deltabeard/DBGC/sw/gb_manager/inc/rom_512kb.gb.h

static const unsigned char rom_512kb_gb[] = {
  0x00, 0xff, 0xff, 0xff, 0xff, 0xff, 0xff, 0xff, 0xff, 0xff, 0xff, 0xff,
  0xff, 0xff, 0xff, 0xff, 0xff, 0xff, 0xff, 0xff, 0xff, 0xff, 0xff, 0xff,
  0xff, 0xff, 0xff, 0xff, 0xff, 0xff, 0xff, 0xff, 0xff, 0xff, 0xff, 0xff,
  0xff, 0xff, 0xff, 0xff, 0xff, 0xff, 0xff, 0xff, 0xff, 0xff, 0xff, 0xff,
  0xff, 0xff, 0xff, 0xff, 0xff, 0xff, 0xff, 0xff, 0xff, 0xff, 0xff, 0xff,
  0xff, 0xff, 0xff, 0xff, 0xff, 0xff, 0xff, 0xff, 0xff, 0xff, 0xff, 0xff,
  0xff, 0xff, 0xff, 0xff, 0xff, 0xff, 0xff, 0xff, 0xff, 0xff, 0xff, 0xff,
  0xff, 0xff, 0xff, 0xff, 0xff, 0xff, 0xff, 0xff, 0xff, 0xff, 0xff, 0xff,
  0xff, 0xff, 0xff, 0xff, 0xff, 0xff, 0xff, 0xff, 0xff, 0xff, 0xff, 0xff,
  0xff, 0xff, 0xff, 0xff, 0xff, 0xff, 0xff, 0xff, 0xff, 0xff, 0xff, 0xff,
  0xff, 0xff, 0xff, 0xff, 0xff, 0xff, 0xff, 0xff, 0xff, 0xff, 0xff, 0xff,
  0xff, 0xff, 0xff, 0xff, 0xff, 0xff, 0xff, 0xff, 0xff, 0xff, 0xff, 0xff,
  0xff, 0xff, 0xff, 0xff, 0xff, 0xff, 0xff, 0xff, 0xff, 0xff, 0xff, 0xff,
  0xff, 0xff, 0xff, 0xff, 0xff, 0xff, 0xff, 0xff, 0xff, 0xff, 0xff, 0xff,
  0xff, 0xff, 0xff, 0xff, 0xff, 0xff, 0xff, 0xff, 0xff, 0xff, 0xff, 0xff,
  0xff, 0xff, 0xff, 0xff, 0xff, 0xff, 0xff, 0xff, 0xff, 0xff, 0xff, 0xff,
  0xff, 0xff, 0xff, 0xff, 0xff, 0xff, 0xff, 0xff, 0xff, 0xff, 0xff, 0xff,
  0xff, 0xff, 0xff, 0xff, 0xff, 0xff, 0xff, 0xff, 0xff, 0xff, 0xff, 0xff,
  0xff, 0xff, 0xff, 0xff, 0xff, 0xff, 0xff, 0xff, 0xff, 0xff, 0xff, 0xff,
  0xff, 0xff, 0xff, 0xff, 0xff, 0xff, 0xff, 0xff, 0xff, 0xff, 0xff, 0xff,
  0xff, 0xff, 0xff, 0xff, 0xff, 0xff, 0xff, 0xff, 0xff, 0xff, 0xff, 0xff,
  0xff, 0xff, 0xff, 0xff, 0x00, 0xc3, 0x50, 0x01, 0xce, 0xed, 0x66, 0x66,
  0xcc, 0x0d, 0x00, 0x0b, 0x03, 0x73, 0x00, 0x83, 0x00, 0x0c, 0x00, 0x0d,
  0x00, 0x08, 0x11, 0x1f, 0x88, 0x89, 0x00, 0x0e, 0xdc, 0xcc, 0x6e, 0xe6,
  0xdd, 0xdd, 0xd9, 0x99, 0xbb, 0xbb, 0x67, 0x63, 0x6e, 0x0e, 0xec, 0xcc,
  0xdd, 0xdc, 0x99, 0x9f, 0xbb, 0xb9, 0x33, 0x3e, 0x6d, 0x6f, 0x6f, 0x6e,
  0x65, 0x79, 0x65, 0x2d, 0x67, 0x62, 0x20, 0x74, 0x65, 0x73, 0x74, 0x00,
  0x5a, 0x5a, 0x00, 0x01, 0x01, 0x00, 0x01, 0x33, 0x00, 0x2b, 0x88, 0x04,
  0x31, 0x00, 0xe0, 0x21, 0x00, 0xc0, 0x11, 0x0e, 0x02, 0x01, 0xa0, 0x00,
  0xcd, 0xda, 0x48, 0x21, 0x00, 0xc2, 0x11, 0xae, 0x02, 0x01, 0x80, 0x01,
  0xcd, 0xda, 0x48, 0xc3, 0x00, 0xc0, 0xf3, 0x21, 0x75, 0x01, 0xc3, 0xf1,
  0x47, 0xcd, 0xf3, 0x48, 0x54, 0x45, 0x53, 0x54, 0x20, 0x46, 0x41, 0x49,
  0x4c, 0x45, 0x44, 0x00, 0xcd, 0xbb, 0x48, 0xf0, 0x83, 0xa7, 0x20, 0x11,
  0xcd, 0xf3, 0x48, 0x24, 0x30, 0x30, 0x30, 0x30, 0x2d, 0x24, 0x33, 0x46,
  0x46, 0x46, 0x00, 0x18, 0x0f, 0xcd, 0xf3, 0x48, 0x24, 0x34, 0x30, 0x30,
  0x30, 0x2d, 0x24, 0x37, 0x46, 0x46, 0x46, 0x00, 0xcd, 0xbb, 0x48, 0xcd,
  0xf3, 0x48, 0x4d, 0x4f, 0x44, 0x45, 0x20, 0x00, 0xf0, 0x84, 0xcd, 0xd0,
  0x48, 0xcd, 0xbb, 0x48, 0xcd, 0xbb, 0x48, 0xcd, 0xf3, 0x48, 0x42, 0x41,
  0x4e, 0x4b, 0x20, 0x4e, 0x55, 0x4d, 0x42, 0x45, 0x52, 0x20, 0x00, 0xf0,
  0x80, 0xcd, 0xd0, 0x48, 0xcd, 0xbb, 0x48, 0xcd, 0xf3, 0x48, 0x45, 0x58,
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
};
static const unsigned int rom_512kb_gb_len = 65536;
