deltabeard/DBGC/sw/gb_manager/inc/2048.gb.h

static const uint8_t __2048_gb[] = {
  0xc9, 0xff, 0xff, 0xff, 0xff, 0xff, 0xff, 0xff, 0xc9, 0xff, 0xff, 0xff,
  0xff, 0xff, 0xff, 0xff, 0xc9, 0xff, 0xff, 0xff, 0xff, 0xff, 0xff, 0xff,
  0xc9, 0xff, 0xff, 0xff, 0xff, 0xff, 0xff, 0xff, 0xc9, 0xff, 0xff, 0xff,
  0xff, 0xff, 0xff, 0xff, 0xff, 0xff, 0xff, 0xff, 0xff, 0xff, 0xff, 0xff,
  0xc9, 0xff, 0xff, 0xff, 0xff, 0xff, 0xff, 0xff, 0xc9, 0xff, 0xff, 0xff,
  0xff, 0xff, 0xff, 0xff, 0xc3, 0x53, 0x01, 0xff, 0xff, 0xff, 0xff, 0xff,
  0xd9, 0xff, 0xff, 0xff, 0xff, 0xff, 0xff, 0xff, 0xd9, 0xff, 0xff, 0xff,
  0xff, 0xff, 0xff, 0xff, 0xd9, 0xff, 0xff, 0xff, 0xff, 0xff, 0xff, 0xff,
  0xd9, 0xff, 0xff, 0xff, 0xff, 0xff, 0xff, 0xff, 0xff, 0xff, 0xff, 0xff,
  0xff, 0xff, 0xff, 0xff, 0xff, 0xff, 0xff, 0xff, 0xff, 0xff, 0xff, 0xff,
  0xff, 0xff, 0xff, 0xff, 0xff, 0xff, 0xff, 0xff, 0xff, 0xff, 0xff, 0xff,
  0xff, 0xff, 0xff, 0xff, 0xff, 0xff, 0xff, 0xff, 0xff, 0xff, 0xff, 0xff,
  0xff, 0xff, 0xff, 0xff, 0xff, 0xff, 0xff, 0xff, 0xff, 0xff, 0xff, 0xff,
  0xff, 0xff, 0xff, 0xff, 0xff, 0xff, 0xff, 0xff, 0xff, 0xff, 0xff, 0xff,
  0xff, 0xff, 0xff, 0xff, 0xff, 0xff, 0xff, 0xff, 0xff, 0xff, 0xff, 0xff,
  0xff, 0xff, 0xff, 0xff, 0xff, 0xff, 0xff, 0xff, 0xff, 0xff, 0xff, 0xff,
  0xff, 0xff, 0xff, 0xff, 0xff, 0xff, 0xff, 0xff, 0xff, 0xff, 0xff, 0xff,
  0xff, 0xff, 0xff, 0xff, 0xff, 0xff, 0xff, 0xff, 0xff, 0xff, 0xff, 0xff,
  0xff, 0xff, 0xff, 0xff, 0xff, 0xff, 0xff, 0xff, 0xff, 0xff, 0xff, 0xff,
  0xff, 0xff, 0xff, 0xff, 0xff, 0xff, 0xff, 0xff, 0xff, 0xff, 0xff, 0xff,
  0xff, 0xff, 0xff, 0xff, 0xff, 0xff, 0xff, 0xff, 0xff, 0xff, 0xff, 0xff,
  0xff, 0xff, 0xff, 0xff, 0x00, 0xc3, 0x50, 0x01, 0xce, 0xed, 0x66, 0x66,
  0xcc, 0x0d, 0x00, 0x0b, 0x03, 0x73, 0x00, 0x83, 0x00, 0x0c, 0x00, 0x0d,
  0x00, 0x08, 0x11, 0x1f, 0x88, 0x89, 0x00, 0x0e, 0xdc, 0xcc, 0x6e, 0xe6,
  0xdd, 0xdd, 0xd9, 0x99, 0xbb, 0xbb, 0x67, 0x63, 0x6e, 0x0e, 0xec, 0xcc,
  0xdd, 0xdc, 0x99, 0x9f, 0xbb, 0xb9, 0x33, 0x3e, 0x32, 0x30, 0x34, 0x38,
  0x2d, 0x67, 0x62, 0x20, 0x20, 0x20, 0x20, 0x58, 0x58, 0x58, 0x58, 0x00,
  0x58, 0x58, 0xff, 0x03, 0x00, 0x01, 0x01, 0x33, 0xff, 0x5d, 0x83, 0x67,
  0xc3, 0x7d, 0x04, 0xf5, 0xc5, 0xd5, 0xe5, 0xf0, 0x96, 0xa7, 0x28, 0x08,
  0xcd, 0x79, 0x01, 0xaf, 0xe0, 0x96, 0x18, 0x03, 0xcd, 0xbb, 0x02, 0xcd,
  0x80, 0xff, 0xcd, 0xad, 0x03, 0x21, 0xf0, 0xff, 0x34, 0xcd, 0xfe, 0x03,
  0xe1, 0xd1, 0xc1, 0xf1, 0xd9, 0x08, 0xfe, 0xcf, 0x31, 0x16, 0xc0, 0x21,
  0x22, 0x98, 0x06, 0x06, 0xd1, 0x7b, 0x22, 0x7a, 0x22, 0xd1, 0x7b, 0x22,
  0x7a, 0x22, 0xd1, 0x7b, 0x22, 0x7a, 0x22, 0xd1, 0x7b, 0x22, 0x7a, 0x22,
  0xd1, 0x7b, 0x22, 0x7a, 0x22, 0xd1, 0x7b, 0x22, 0x7a, 0x22, 0xd1, 0x7b,
  0x22, 0x7a, 0x22, 0xd1, 0x7b, 0x22, 0x7a, 0x22, 0x11, 0x10, 0x00, 0x19,
  0xe8, 0x04, 0xd1, 0x7b, 0x22, 0x7a, 0x22, 0xd1, 0x7b, 0x22, 0x7a, 0x22,
  0xd1, 0x7b, 0x22, 0x7a, 0x22, 0xd1, 0x7b, 0x22, 0x7a, 0x22, 0xd1, 0x7b,
  0x22, 0x7a, 0x22, 0xd1, 0x7b, 0x22, 0x7a, 0x22, 0xd1, 0x7b, 0x22, 0x7a,
  0x22, 0xd1, 0x7b, 0x22, 0x7a, 0x22, 0x11, 0x10, 0x00, 0x19, 0xe8, 0x04,
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
};
static const unsigned int __2048_gb_len = 11920;
