deltabeard/DBGC/sw/gb_manager/inc/gb_manager.gb.h

static const unsigned char gb_manager_gb[] = {
  0xff, 0xff, 0xff, 0xff, 0xff, 0xff, 0xff, 0xff, 0xff, 0xff, 0xff, 0xff,
  0xff, 0xff, 0xff, 0xff, 0xff, 0xff, 0xff, 0xff, 0xff, 0xff, 0xff, 0xff,
  0xff, 0xff, 0xff, 0xff, 0xff, 0xff, 0xff, 0xff, 0xe9, 0xff, 0xff, 0xff,
  0xff, 0xff, 0xff, 0xff, 0x22, 0x0d, 0x20, 0xfc, 0xc9, 0xff, 0xff, 0xff,
  0x1a, 0x22, 0x13, 0x0d, 0x20, 0xfa, 0xc9, 0xff, 0xff, 0xff, 0xff, 0xff,
  0xff, 0xff, 0xff, 0xff, 0xf5, 0xe5, 0x21, 0xa4, 0xc0, 0xc3, 0x80, 0x00,
  0xc3, 0xf8, 0x0b, 0xff, 0xff, 0xff, 0xff, 0xff, 0xff, 0xff, 0xff, 0xff,
  0xff, 0xff, 0xff, 0xff, 0xff, 0xff, 0xff, 0xff, 0xff, 0xff, 0xff, 0xff,
  0xff, 0xff, 0xff, 0xff, 0xff, 0xff, 0xff, 0xff, 0xff, 0xff, 0xff, 0xff,
  0xff, 0xff, 0xff, 0xff, 0xff, 0xff, 0xff, 0xff, 0xff, 0xff, 0xff, 0xff,
  0xff, 0xff, 0xff, 0xff, 0xff, 0xff, 0xff, 0xff, 0xc5, 0xd5, 0x2a, 0xb6,
  0x28, 0x0b, 0xe5, 0x3a, 0x6e, 0x67, 0xe7, 0xe1, 0x23, 0x18, 0xf3, 0xe8,
  0x04, 0xd1, 0xc1, 0xe1, 0xf0, 0x41, 0xe6, 0x02, 0x20, 0xfa, 0xf1, 0xd9,
  0x21, 0xa2, 0xc0, 0x34, 0x20, 0x02, 0x23, 0x34, 0xcd, 0x80, 0xff, 0x3e,
  0x01, 0xe0, 0x91, 0xc9, 0xff, 0xff, 0xff, 0xff, 0xff, 0xff, 0xff, 0xff,
  0xff, 0xff, 0xff, 0xff, 0xff, 0xff, 0xff, 0xff, 0xff, 0xff, 0xff, 0xff,
  0xff, 0xff, 0xff, 0xff, 0xff, 0xff, 0xff, 0xff, 0xff, 0xff, 0xff, 0xff,
  0xff, 0xff, 0xff, 0xff, 0xff, 0xff, 0xff, 0xff, 0xff, 0xff, 0xff, 0xff,
  0xff, 0xff, 0xff, 0xff, 0xff, 0xff, 0xff, 0xff, 0xff, 0xff, 0xff, 0xff,
  0xff, 0xff, 0xff, 0xff, 0xff, 0xff, 0xff, 0xff, 0xff, 0xff, 0xff, 0xff,
  0xff, 0xff, 0xff, 0xff, 0xff, 0xff, 0xff, 0xff, 0xff, 0xff, 0xff, 0xff,
  0xff, 0xff, 0xff, 0xff, 0xc3, 0x53, 0x01, 0xce, 0xce, 0xed, 0x66, 0x66,
  0xcc, 0x0d, 0x00, 0x0b, 0x03, 0x73, 0x00, 0x83, 0x00, 0x0c, 0x00, 0x0d,
  0x00, 0x08, 0x11, 0x1f, 0x88, 0x89, 0x00, 0x0e, 0xdc, 0xcc, 0x6e, 0xe6,
  0xdd, 0xdd, 0xd9, 0x99, 0xbb, 0xbb, 0x67, 0x63, 0x6e, 0x0e, 0xec, 0xcc,
  0xdd, 0xdc, 0x99, 0x9f, 0xbb, 0xb9, 0x33, 0x3e, 0x47, 0x42, 0x4d, 0x47,
  0x52, 0x00, 0x00, 0x00, 0x00, 0x00, 0x00, 0x00, 0x00, 0x00, 0x00, 0x00,
  0x30, 0x30, 0x00, 0x00, 0x00, 0x00, 0x00, 0x33, 0x01, 0xe4, 0x86, 0xb6,
  0xfa, 0xa0, 0xc0, 0xf3, 0x57, 0x31, 0x00, 0xe0, 0x3e, 0xc0, 0xe0, 0x92,
  0x67, 0xaf, 0x6f, 0x0e, 0xa0, 0xef, 0x21, 0xa0, 0xc0, 0x0e, 0x18, 0xef,
  0x7a, 0xea, 0xa0, 0xc0, 0xcd, 0x4c, 0x08, 0xaf, 0xe0, 0x42, 0xe0, 0x43,
  0xe0, 0x41, 0xe0, 0x4a, 0x3e, 0x07, 0xe0, 0x4b, 0x11, 0xc7, 0x01, 0x21,
  0x80, 0xff, 0x0e, 0x0c, 0xf7, 0xcd, 0x80, 0xff, 0x01, 0x9c, 0x00, 0xcd,
  0x2f, 0x08, 0x3e, 0xe4, 0xe0, 0x47, 0xe0, 0x48, 0x3e, 0x1b, 0xe0, 0x49,
  0x3e, 0xc0, 0xe0, 0x40, 0xaf, 0xe0, 0x0f, 0x3e, 0x01, 0xe0, 0xff, 0xe0,
  0x90, 0xaf, 0x21, 0xa2, 0xc0, 0x22, 0x77, 0xe0, 0x26, 0xcd, 0xfb, 0x0f,
  0xfb, 0xcd, 0xaa, 0x07, 0x76, 0x00, 0x18, 0xfc, 0xfb, 0xc9, 0xf3, 0xc9,
  0xf3, 0xf8, 0x02, 0xaf, 0xe0, 0x0f, 0x7e, 0xfb, 0xe0, 0xff, 0xc9, 0xf0,
  0x92, 0xb7, 0xc8, 0xe0, 0x46, 0x3e, 0x28, 0x3d, 0x20, 0xfd, 0xc9, 0xff,
  0xff, 0xff, 0xff, 0xff, 0xff, 0xff, 0xff, 0xff, 0xff, 0xff, 0xff, 0xff,
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
};
unsigned int gb_manager_gb_len = 4112;
