deltabeard/DBGC/sw/gb_manager/inc/libbet.gb.h

static const uint8_t libbet_gb[] = {
  0xff, 0x7f, 0xb5, 0x56, 0x6b, 0x2d, 0x00, 0x00, 0x1a, 0x13, 0x37, 0x17,
  0x47, 0x30, 0x04, 0xf0, 0x80, 0x18, 0x04, 0x1a, 0x13, 0xe0, 0x80, 0x22,
  0x79, 0xcb, 0x20, 0x38, 0x03, 0x1a, 0x13, 0x4f, 0x22, 0xcb, 0x20, 0x20,
  0xe8, 0xc9, 0xaf, 0xe0, 0x80, 0x4f, 0xc5, 0xcd, 0x08, 0x00, 0xcd, 0x08,
  0x00, 0x79, 0xc1, 0x4f, 0x05, 0x20, 0xf3, 0xc9, 0xf0, 0x44, 0xfe, 0x90,
  0x30, 0xfa, 0xc9, 0xff, 0xf5, 0xfa, 0xa1, 0xc4, 0x3c, 0xc3, 0x65, 0x32,
  0xd9, 0xff, 0x2c, 0x00, 0x9c, 0x00, 0x07, 0x01, 0x6b, 0x01, 0xc9, 0x01,
  0x23, 0x02, 0x77, 0x02, 0xc7, 0x02, 0x12, 0x03, 0x58, 0x03, 0x9b, 0x03,
  0xda, 0x03, 0x16, 0x04, 0x4e, 0x04, 0x83, 0x04, 0xb5, 0x04, 0xe5, 0x04,
  0x11, 0x05, 0x3b, 0x05, 0x63, 0x05, 0x89, 0x05, 0xac, 0x05, 0xce, 0x05,
  0xed, 0x05, 0x0b, 0x06, 0x27, 0x06, 0x42, 0x06, 0x5b, 0x06, 0x72, 0x06,
  0x89, 0x06, 0x9e, 0x06, 0xb2, 0x06, 0xc4, 0x06, 0xd6, 0x06, 0xe7, 0x06,
  0xf7, 0x06, 0x06, 0x07, 0x14, 0x07, 0x21, 0x07, 0x2d, 0x07, 0x39, 0x07,
  0x44, 0x07, 0x4f, 0x07, 0x59, 0x07, 0x62, 0x07, 0x6b, 0x07, 0x73, 0x07,
  0x7b, 0x07, 0x83, 0x07, 0x8a, 0x07, 0x90, 0x07, 0x97, 0x07, 0x9d, 0x07,
  0xa2, 0x07, 0xa7, 0x07, 0xac, 0x07, 0xb1, 0x07, 0xb6, 0x07, 0xba, 0x07,
  0xbe, 0x07, 0xc1, 0x07, 0xc5, 0x07, 0xc8, 0x07, 0xcb, 0x07, 0x3e, 0x10,
  0xcd, 0xea, 0x00, 0x47, 0x3e, 0x20, 0xcd, 0xea, 0x00, 0xcb, 0x37, 0xa8,
  0x47, 0x3e, 0x30, 0xe0, 0x00, 0xfa, 0x9f, 0xc5, 0xa8, 0xa0, 0xea, 0xa0,
  0xc5, 0x78, 0xea, 0x9f, 0xc5, 0xc9, 0xe0, 0x00, 0xcd, 0xf7, 0x00, 0xf0,
  0x00, 0xf0, 0x00, 0xf0, 0x00, 0xf6, 0xf0, 0xc9, 0x22, 0x3c, 0x0d, 0x20,
  0xfb, 0xc9, 0xff, 0xff, 0x00, 0xc3, 0x0f, 0x33, 0xce, 0xed, 0x66, 0x66,
  0xcc, 0x0d, 0x00, 0x0b, 0x03, 0x73, 0x00, 0x83, 0x00, 0x0c, 0x00, 0x0d,
  0x00, 0x08, 0x11, 0x1f, 0x88, 0x89, 0x00, 0x0e, 0xdc, 0xcc, 0x6e, 0xe6,
  0xdd, 0xdd, 0xd9, 0x99, 0xbb, 0xbb, 0x67, 0x63, 0x6e, 0x0e, 0xec, 0xcc,
  0xdd, 0xdc, 0x99, 0x9f, 0xbb, 0xb9, 0x33, 0x3e, 0x4c, 0x49, 0x42, 0x42,
  0x45, 0x54, 0x00, 0x00, 0x00, 0x00, 0x00, 0x00, 0x00, 0x00, 0x00, 0x80,
  0x4f, 0x4b, 0x03, 0x00, 0x00, 0x00, 0x01, 0x33, 0x00, 0xe4, 0x89, 0xff,
  0x00, 0x00, 0x00, 0x00, 0x00, 0x00, 0x00, 0x00, 0x00, 0x80, 0x80, 0x80,
  0x80, 0x00, 0x80, 0x00, 0x00, 0xa0, 0xa0, 0x00, 0x00, 0x00, 0x00, 0x00,
  0x00, 0x50, 0xf8, 0x50, 0xf8, 0x50, 0x00, 0x00, 0x00, 0x20, 0x70, 0xa0,
  0x60, 0x50, 0xe0, 0x40, 0x00, 0xd0, 0xd0, 0x20, 0x60, 0x40, 0xb0, 0xb0,
  0x00, 0x40, 0xa0, 0x40, 0xa8, 0x90, 0x68, 0x00, 0x00, 0x80, 0x80, 0x00,
  0x00, 0x00, 0x00, 0x00, 0x00, 0x20, 0x40, 0x80, 0x80, 0x80, 0x40, 0x20,
  0x00, 0x80, 0x40, 0x20, 0x20, 0x20, 0x40, 0x80, 0x00, 0x20, 0xa8, 0x70,
  0xa8, 0x20, 0x00, 0x00, 0x00, 0x20, 0x20, 0xf8, 0x20, 0x20, 0x00, 0x00,
  0x00, 0x00, 0x00, 0x00, 0x00, 0x00, 0x80, 0x80, 0x00, 0x00, 0x00, 0xf0,
  0x00, 0x00, 0x00, 0x00, 0x00, 0x00, 0x00, 0x00, 0x00, 0x00, 0x80, 0x00,
  0x00, 0x10, 0x10, 0x20, 0x60, 0x40, 0x80, 0x80, 0x00, 0x60, 0x90, 0x90,
  0x90, 0x90, 0x60, 0x00, 0x00, 0x20, 0x60, 0x20, 0x20, 0x20, 0x20, 0x00,
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
};
const unsigned int libbet_gb_len = 13579;
